watterott/Wattuino/software/SAM-BAR/src/config/conf_usb.h

/**
 * \file
 *
 * \brief USB configuration file
 *
 * Copyright (c) 2011-2015 Atmel Corporation. All rights reserved.
 *
 * \asf_license_start
 *
 * \page License
 *
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
 * 3. The name of Atmel may not be used to endorse or promote products derived
 *    from this software without specific prior written permission.
 *
 * 4. This software may only be redistributed and used in connection with an
 *    Atmel microcontroller product.
 *
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
 * \asf_license_stop
 *
 */

#ifndef _CONF_USB_H_
#define _CONF_USB_H_

#include "compiler.h"
#include "conf_board.h"

/**
 * USB Device Configuration
 * @{
 */

#define  USB_DEVICE_MAJOR_VERSION         1
#define  USB_DEVICE_MINOR_VERSION         0
#define  USB_DEVICE_POWER                 20 // Consumption on Vbus line (mA)
#define  USB_DEVICE_ATTR                  \
	(USB_CONFIG_ATTR_BUS_POWERED)
//	(USB_CONFIG_ATTR_SELF_POWERED)
//	(USB_CONFIG_ATTR_REMOTE_WAKEUP|USB_CONFIG_ATTR_SELF_POWERED)
//	(USB_CONFIG_ATTR_REMOTE_WAKEUP|USB_CONFIG_ATTR_BUS_POWERED)

/**
 * Device speeds support
 * Low speed not supported by CDC and MSC
 * @{
 */

//! To define a Low speed device
//#define  USB_DEVICE_LOW_SPEED

//! To authorize the High speed
#if (UC3A3||UC3A4)
#  define  USB_DEVICE_HS_SUPPORT
#elif (SAM3XA||SAM3U)
#  define  USB_DEVICE_HS_SUPPORT
#endif
//@}


/**
 * USB Device Callbacks definitions (Optional)
 * @{
 */
#define  UDC_VBUS_EVENT(b_vbus_high)
#define  UDC_SOF_EVENT()                  main_sof_action()
#define  UDC_SUSPEND_EVENT()              //main_suspend_action()
#define  UDC_RESUME_EVENT()               //main_resume_action()
//! Mandatory when USB_DEVICE_ATTR authorizes remote wakeup feature
// #define  UDC_REMOTEWAKEUP_ENABLE()        user_callback_remotewakeup_enable()
// extern void user_callback_remotewakeup_enable(void);
// #define  UDC_REMOTEWAKEUP_DISABLE()       user_callback_remotewakeup_disable()
// extern void user_callback_remotewakeup_disable(void);
//! When a extra string descriptor must be supported
//! other than manufacturer, product and serial string
//#define  UDC_GET_EXTRA_STRING()           main_extra_string()
//@}

/**
 * USB Device low level configuration
 * When only one interface is used, these configurations are defined by the class module.
 * For composite device, these configuration must be defined here
 * @{
 */
//! Control endpoint size
#define  USB_DEVICE_EP_CTRL_SIZE       64

//! Two interfaces for this device (CDC COM + CDC DATA + MSC)
#define  USB_DEVICE_NB_INTERFACE       3

//! 5 endpoints used by CDC and MSC interfaces
#if SAM3U
// (3 | USB_EP_DIR_IN)  // CDC Notify endpoint
// (6 | USB_EP_DIR_IN)  // CDC TX
// (5 | USB_EP_DIR_OUT) // CDC RX
// (1 | USB_EP_DIR_IN)  // MSC IN
// (2 | USB_EP_DIR_OUT) // MSC OUT
#  define  USB_DEVICE_MAX_EP           6
#  if defined(USB_DEVICE_HS_SUPPORT)
// In HS mode, size of bulk endpoints are 512
// If CDC and MSC endpoints all uses 2 banks, DPRAM is not enough: 4 bulk
// endpoints requires 4K bytes. So reduce the number of banks of CDC bulk
// endpoints to use less DPRAM. Keep MSC setting to keep MSC performance.
#     define  UDD_BULK_NB_BANK(ep) ((ep == 5 || ep== 6) ? 1 : 2)
#endif
#else
// (3 | USB_EP_DIR_IN)  // CDC Notify endpoint
// (4 | USB_EP_DIR_IN)  // CDC TX
// (5 | USB_EP_DIR_OUT) // CDC RX
// (1 | USB_EP_DIR_IN)  // MSC IN
// (2 | USB_EP_DIR_OUT) // MSC OUT
#  define  USB_DEVICE_MAX_EP           5
#  if SAM3XA && defined(USB_DEVICE_HS_SUPPORT)
// In HS mode, size of bulk endpoints are 512
// If CDC and MSC endpoints all uses 2 banks, DPRAM is not enough: 4 bulk
// endpoints requires 4K bytes. So reduce the number of banks of CDC bulk
// endpoints to use less DPRAM. Keep MSC setting to keep MSC performance.
#     define  UDD_BULK_NB_BANK(ep) ((ep == 4 || ep== 5) ? 1 : 2)
#  endif
#endif
//@}

//@}


/**
 * USB Interface Configuration
 * @{
 */
/**
 * Configuration of CDC interface
 * @{
 */

//! Define two USB communication ports
#define  UDI_CDC_PORT_NB 1

//! Interface callback definition
#define  UDI_CDC_ENABLE_EXT(port)         main_cdc_enable(port)
#define  UDI_CDC_DISABLE_EXT(port)        main_cdc_disable(port)
#define  UDI_CDC_RX_NOTIFY(port)          //main_cdc_rx_notify(port)
#define  UDI_CDC_TX_EMPTY_NOTIFY(port)
#define  UDI_CDC_SET_CODING_EXT(port,cfg) //main_cdc_set_coding(port, cfg)  // Baudrate etc.
#define  UDI_CDC_SET_DTR_EXT(port,set)    //main_cdc_set_dtr(port,set)
#define  UDI_CDC_SET_RTS_EXT(port,set)

//! Define it when the transfer CDC Device to Host is a low rate (<512000 bauds)
//! to reduce CDC buffers size
//#define  UDI_CDC_LOW_RATE

//! Default configuration of communication port
#define  UDI_CDC_DEFAULT_RATE             115200
#define  UDI_CDC_DEFAULT_STOPBITS         CDC_STOP_BITS_1
#define  UDI_CDC_DEFAULT_PARITY           CDC_PAR_NONE
#define  UDI_CDC_DEFAULT_DATABITS         8

//! Enable id string of interface to add an extra USB string
#define  UDI_CDC_IAD_STRING_ID            4

/**
 * USB CDC low level configuration
 * In standalone these configurations are defined by the CDC module.
 * For composite device, these configuration must be defined here
 * @{
 */
//! Endpoint numbers definition
#if SAM3U
#  define  UDI_CDC_COMM_EP_0             (3 | USB_EP_DIR_IN) // Notify endpoint
#  define  UDI_CDC_DATA_EP_IN_0          (6 | USB_EP_DIR_IN) // TX
#  define  UDI_CDC_DATA_EP_OUT_0         (5 | USB_EP_DIR_OUT)// RX
#else
#  define  UDI_CDC_COMM_EP_0             (3 | USB_EP_DIR_IN) // Notify endpoint
#  define  UDI_CDC_DATA_EP_IN_0          (4 | USB_EP_DIR_IN) // TX
#  define  UDI_CDC_DATA_EP_OUT_0         (5 | USB_EP_DIR_OUT)// RX
#endif

//! Interface numbers
#define  UDI_CDC_COMM_IFACE_NUMBER_0   0
#define  UDI_CDC_DATA_IFACE_NUMBER_0   1
//@}
//@}


/**
 * Configuration of MSC interface
 * @{
 */
//! Vendor name and Product version of MSC interface
#define UDI_MSC_GLOBAL_VENDOR_ID            \
   'B', 'O', 'O', 'T', 'L', 'D', 'R', ' '
#define UDI_MSC_GLOBAL_PRODUCT_VERSION            \
   '1', '.', '0', '0'

//! Interface callback definition
#define  UDI_MSC_ENABLE_EXT()          main_msc_enable()
#define  UDI_MSC_DISABLE_EXT()         main_msc_disable()

//! Enable id string of interface to add an extra USB string
#define  UDI_MSC_STRING_ID                2 // 5

/**
 * USB MSC low level configuration
 * In standalone these configurations are defined by the MSC module.
 * For composite device, these configuration must be defined here
 * @{
 */
//! Endpoint numbers definition
#define  UDI_MSC_EP_IN                 (1 | USB_EP_DIR_IN)
#define  UDI_MSC_EP_OUT                (2 | USB_EP_DIR_OUT)

//! Interface number
#define  UDI_MSC_IFACE_NUMBER          2
//@}
//@}

//@}


/**
 * Description of Composite Device
 * @{
 */
//! USB Interfaces descriptor structure
#define UDI_COMPOSITE_DESC_T \
	usb_iad_desc_t       udi_cdc_iad; \
	udi_cdc_comm_desc_t  udi_cdc_comm; \
	udi_cdc_data_desc_t  udi_cdc_data; \
	udi_msc_desc_t       udi_msc

//! USB Interfaces descriptor value for Full Speed
#define UDI_COMPOSITE_DESC_FS \
	.udi_cdc_iad   = UDI_CDC_IAD_DESC_0, \
	.udi_cdc_comm  = UDI_CDC_COMM_DESC_0, \
	.udi_cdc_data  = UDI_CDC_DATA_DESC_0_FS, \
	.udi_msc       = UDI_MSC_DESC_FS

//! USB Interfaces descriptor value for High Speed
#define UDI_COMPOSITE_DESC_HS \
	.udi_cdc_iad   = UDI_CDC_IAD_DESC_0, \
	.udi_cdc_comm  = UDI_CDC_COMM_DESC_0, \
	.udi_cdc_data  = UDI_CDC_DATA_DESC_0_HS, \
	.udi_msc       = UDI_MSC_DESC_HS

//! USB Interface APIs
#define UDI_COMPOSITE_API \
	&udi_api_cdc_comm, \
	&udi_api_cdc_data, \
	&udi_api_msc
//@}


/**
 * USB Device Driver Configuration
 * @{
 */
#define UDD_CLOCK_GEN      GCLK_GENERATOR_0
//@}

//! The includes of classes and other headers must be done at the end of this file to avoid compile error
#include "udi_cdc.h"
#include "udi_msc.h"
#include "main.h"


#endif // _CONF_USB_H_
