watterott/Wattuino/software/SAM-BAR/src/virtual_flash_mem.c

/**
 * \file
 *
 * \brief Management of the virtual memory.
 * Copyright (c) 2009 - 2013 Atmel Corporation. All rights reserved.
 *
 * \asf_license_start
 *
 * \page License
 *
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
 * 3. The name of Atmel may not be used to endorse or promote products derived
 *    from this software without specific prior written permission.
 *
 * 4. This software may only be redistributed and used in connection with an
 *    Atmel microcontroller product.
 *
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
 * \asf_license_stop
 *
 */

/**
 * \defgroup group_common_components_memory_virtual_mem Virtual Memory in RAM
 *
 * The component manages a disk on a volatile memory (internal RAM).
 * This can be connected to a File System management or a USB Device
 * Mass Storage Interface via the service Memory Control Access.
 *
 * \{
 */

//_____  I N C L U D E S ___________________________________________________

#include "conf_access.h"
#include "conf_virtual_flash_mem.h"


#if VIRTUAL_FLASH_MEM == ENABLE

#include "virtual_flash_mem.h"


#ifndef VMEM_NB_SECTOR
#  error Define VMEM_NB_SECTOR in conf_virtual_flash_mem.h file
#endif

//_____ M A C R O S ________________________________________________________

//_____ P R I V A T E   D E C L A R A T I O N S ____________________________


//_____ D E F I N I T I O N S ______________________________________________

/* File Data Buffer */
COMPILER_WORD_ALIGNED
uint8_t BlockBuffer[VMEM_SECTOR_SIZE];

bool b_vmem_unloaded = false;

//_____ D E C L A R A T I O N S ____________________________________________

//! This function tests memory state, and starts memory initialization
//! @return                            Ctrl_status
//!   It is ready                ->    CTRL_GOOD
//!   Memory unplug              ->    CTRL_NO_PRESENT
//!   Not initialized or changed ->    CTRL_BUSY
//!   An error occurred          ->    CTRL_FAIL
Ctrl_status virtual_test_unit_ready(void)
{
	return b_vmem_unloaded ? CTRL_NO_PRESENT : CTRL_GOOD;
}


//! This function returns the address of the last valid sector
//! @param uint32_t_nb_sector  Pointer to number of sectors (sector=512 bytes)
//! @return                            Ctrl_status
//!   It is ready                ->    CTRL_GOOD
//!   Memory unplug              ->    CTRL_NO_PRESENT
//!   Not initialized or changed ->    CTRL_BUSY
//!   An error occurred          ->    CTRL_FAIL
Ctrl_status virtual_read_capacity(uint32_t *uint32_t_nb_sector)
{
	if (b_vmem_unloaded) {
		return CTRL_NO_PRESENT;
	}

	if (VMEM_NB_SECTOR<8) {
		*uint32_t_nb_sector = 8-1;
	} else {
		*uint32_t_nb_sector = VMEM_NB_SECTOR- 1;
	}
	return CTRL_GOOD;
}


//! This function returns the write-protected mode
//!
//! @return true if the memory is protected
//!
bool virtual_wr_protect(void)
{
	return false;
}


//! This function informs about the memory type
//!
//! @return true if the memory is removable
//!
bool virtual_removal(void)
{
	return true;
}


//! This function unloads/loads the memory
//!
//! @return true if the memory is unloaded
//!
bool virtual_unload(bool unload)
{
	b_vmem_unloaded = unload;
	return true;
}

//------------ SPECIFIC FUNCTIONS FOR TRANSFER BY USB -------------------------

#if ACCESS_USB == true

#include "udi_msc.h"

//! This function transfers the data between memory and USB MSC interface
//!
//! @param addr         Sector address to start read
//! @param nb_sector    Number of sectors to transfer (sector=512 bytes)
//! @param b_read       Memory to USB, if true
//!
//! @return                            Ctrl_status
//!   It is ready                ->    CTRL_GOOD
//!   Memory unplug              ->    CTRL_NO_PRESENT
//!   Not initialized or changed ->    CTRL_BUSY
//!   An error occurred          ->    CTRL_FAIL
//!
static Ctrl_status virtual_usb_trans(uint32_t addr, uint16_t nb_sector, bool b_read)
{
	if ((addr > VMEM_NB_SECTOR) ||  (addr + nb_sector > VMEM_NB_SECTOR)) {
		return CTRL_FAIL;
	}

	for (uint16_t i = 0; i < nb_sector; i++)
	{
		if (b_read) {
			VirtualFAT_ReadBlock(addr + i);
			if (!udi_msc_trans_block(b_read, BlockBuffer, VMEM_SECTOR_SIZE, NULL)) {
				return CTRL_FAIL; // transfer aborted
			}
		} else {
			if (!udi_msc_trans_block(b_read, BlockBuffer, VMEM_SECTOR_SIZE, NULL)) {
				return CTRL_FAIL; // transfer aborted
			}
			VirtualFAT_WriteBlock(addr + i);
		}
	}

	return CTRL_GOOD;
}

//! This function transfers the memory data to the USB MSC interface
//!
//! @param addr         Sector address to start read
//! @param nb_sector    Number of sectors to transfer (sector=512 bytes)
//!
//! @return                            Ctrl_status
//!   It is ready                ->    CTRL_GOOD
//!   Memory unplug              ->    CTRL_NO_PRESENT
//!   Not initialized or changed ->    CTRL_BUSY
//!   An error occurred          ->    CTRL_FAIL
//!
Ctrl_status virtual_usb_read_10(uint32_t addr, uint16_t nb_sector)
{
	return virtual_usb_trans(addr, nb_sector, true);
}


//! This function transfers the USB MSC data to the memory
//!
//! @param addr         Sector address to start write
//! @param nb_sector    Number of sectors to transfer (sector=512 bytes)
//!
//! @return                            Ctrl_status
//!   It is ready                ->    CTRL_GOOD
//!   Memory unplug              ->    CTRL_NO_PRESENT
//!   Not initialized or changed ->    CTRL_BUSY
//!   An error occurred          ->    CTRL_FAIL
//!
Ctrl_status virtual_usb_write_10(uint32_t addr, uint16_t nb_sector)
{
	return virtual_usb_trans(addr, nb_sector, false);
}

#endif  // ACCESS_USB == true

#endif  // VIRTUAL_MEM == ENABLE

/**
 * \}
 */
